ios-cv/maxbox/firmware/main/led.h

/* LED functions
*/
#pragma once

#ifdef __cplusplus
extern "C" {
#endif

typedef enum {IDLE, HEARTBEAT, PROCESSING, LOCKING, UNLOCKING, DENY, ERROR, FIRMWARE} led_status_t;

void led_init(void);
void led_update(led_status_t);
void led_loop(void *args);

#ifdef __cplusplus
}
#endif
